haShinui/usb_pd/KiCad Files/CYPD3177_DEV_BOARD/pictures/CYPD3177_3.3V_V2_+_OLED.png

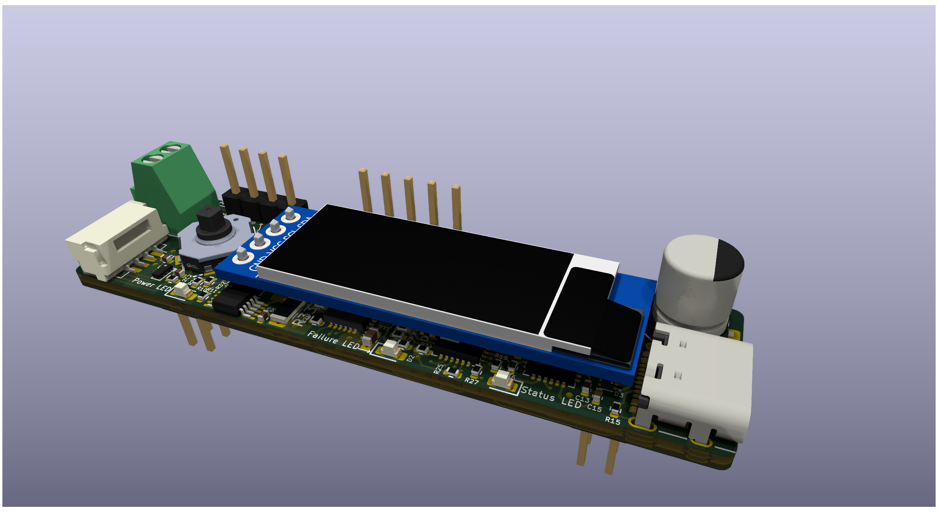
KiCad Files/CYPD3177_DEV_BOARD/pictures/CYPD3177_3.3V_V2_+_OLED.png
