haShinui/usb_pd/KiCad Files/CYPD3177_DEV_BOARD/pictures/new_v2/Screenshot 2025-05-14 235045.png

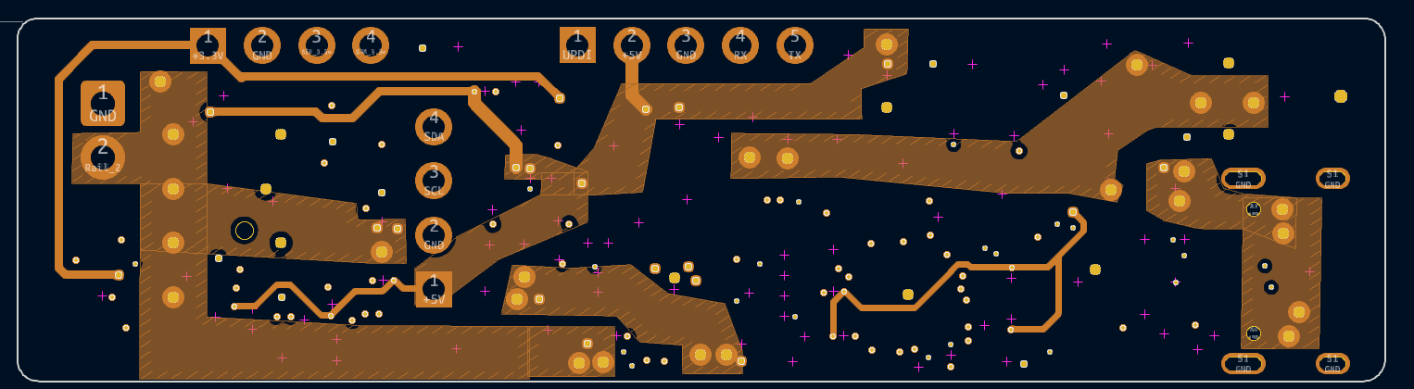
KiCad Files/CYPD3177_DEV_BOARD/pictures/new_v2/Screenshot 2025-05-14 235045.png
