haShinui/usb_pd/KiCad Files/CYPD3177_DEV_BOARD/pictures/Screenshot 2025-05-13 152915.png

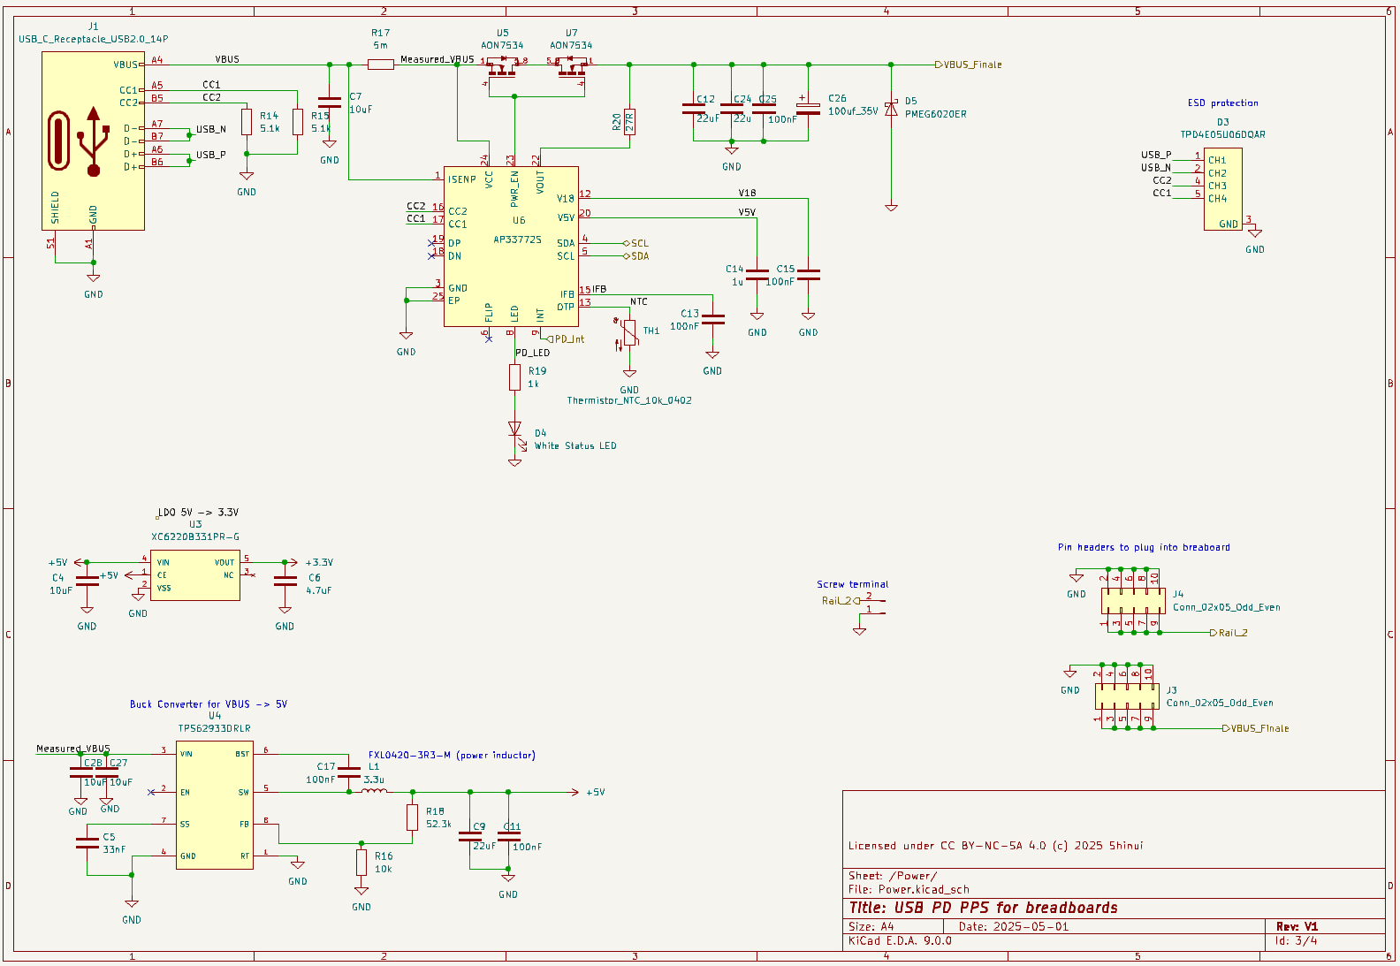
KiCad Files/CYPD3177_DEV_BOARD/pictures/Screenshot 2025-05-13 152915.png
