haShinui/usb_pd/KiCad Files/CYPD3177_DEV_BOARD/TPS16630/TPS16630RGER.STEP

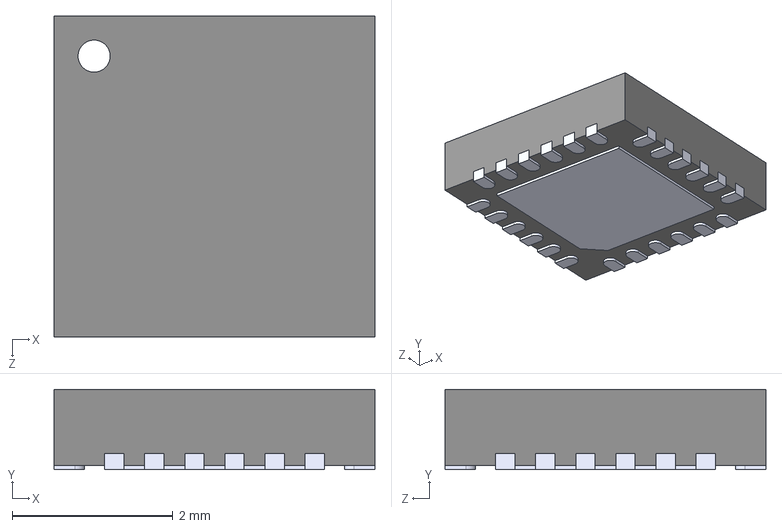
[picture p32: CAD file, 2025-05-05]
KiCad Files/CYPD3177_DEV_BOARD/TPS16630/TPS16630RGER.STEP
4.00 x 1.00 x 4.00 mm
