haShinui/usb_pd/KiCad Files/CYPD3177_DEV_BOARD/TPS22992S/TPS22992SRXNR--3DModel-STEP-56544.STEP

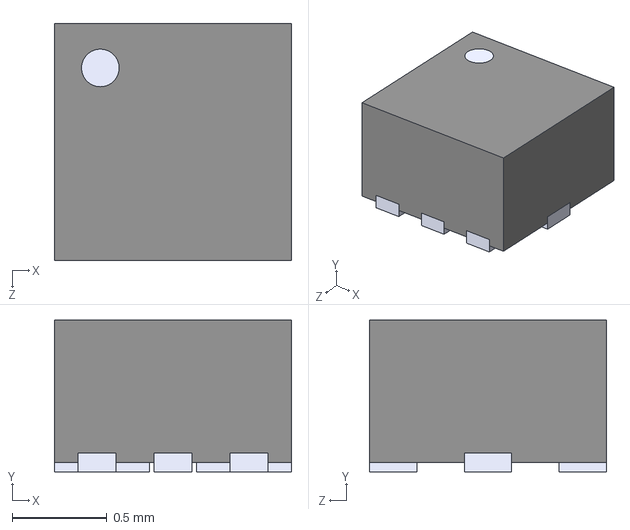
[picture p33: CAD file, 2025-05-05]
KiCad Files/CYPD3177_DEV_BOARD/TPS22992S/TPS22992SRXNR--3DModel-STEP-56544.STEP
1.25 x 0.8 x 1.25 mm
